fabPlane/playbridge-ps1-wireless-adapter/docs/diagrams/ps1-contact-allocation.png

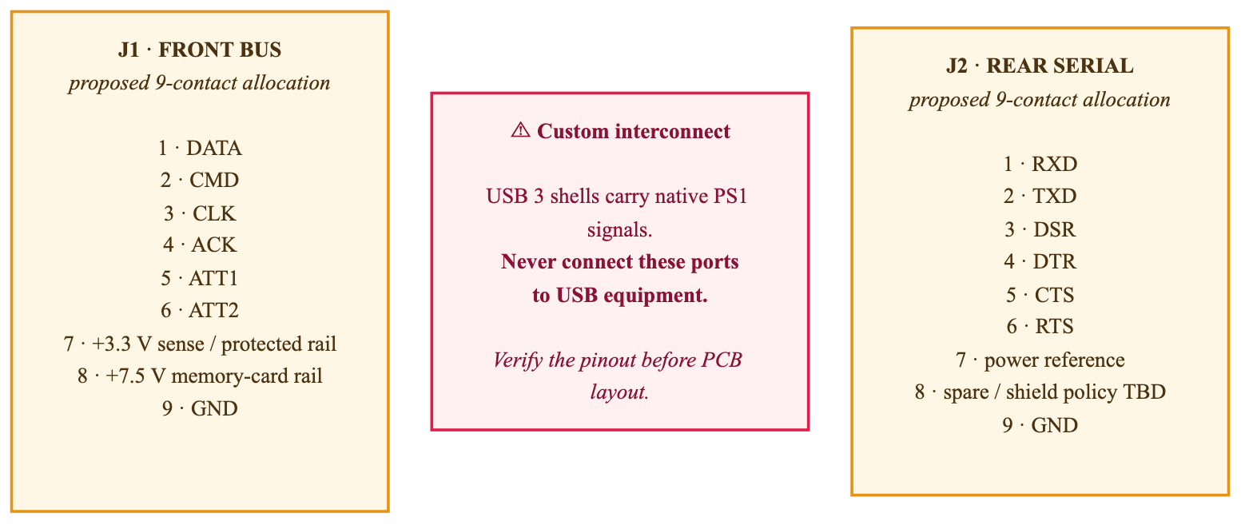
docs/diagrams/ps1-contact-allocation.png
