fabPlane/playbridge-ps1-wireless-adapter/docs/diagrams/ps1-front-harness.png

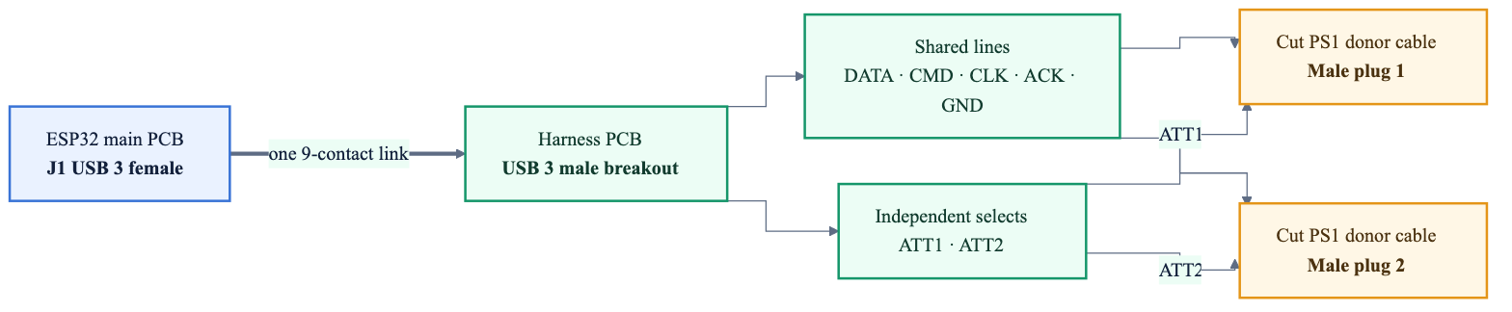
docs/diagrams/ps1-front-harness.png
