fabPlane/playbridge-ps1-wireless-adapter/docs/diagrams/ps1-modular-interconnect.png

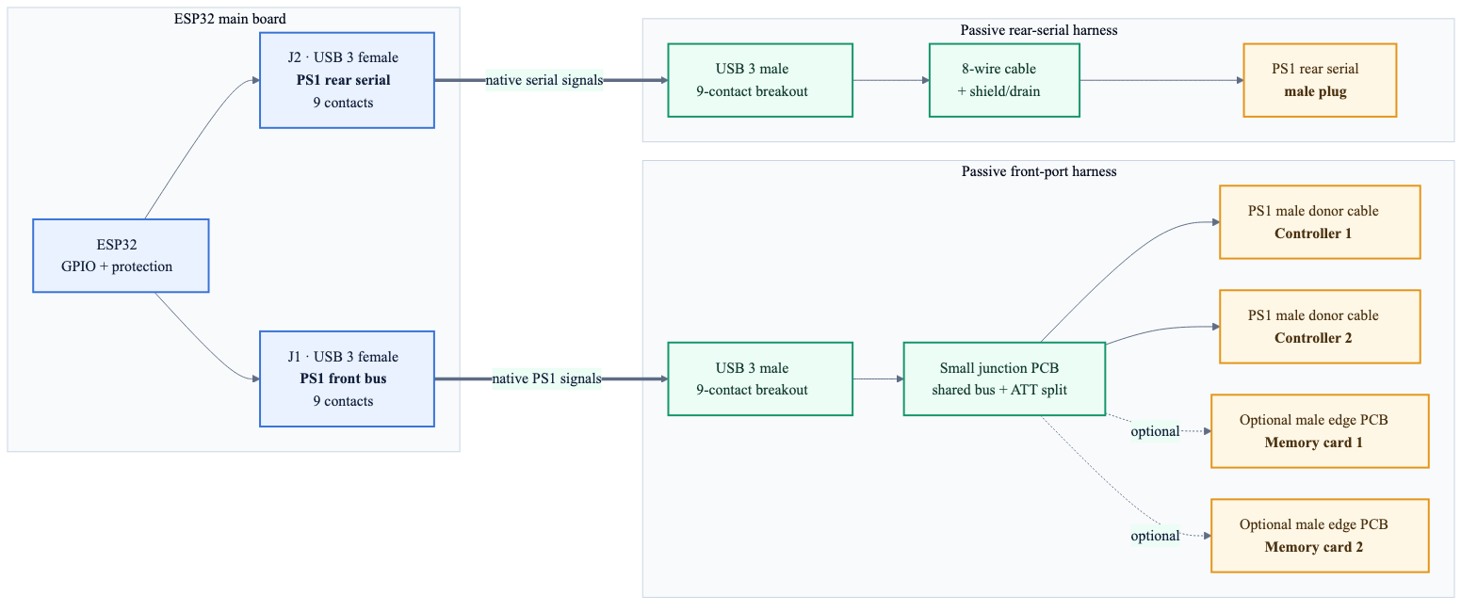
docs/diagrams/ps1-modular-interconnect.png
