fabPlane/playbridge-ps1-wireless-adapter/versions/v1-pcb-mounted-pin-array/docs/images/current/full-board-top-orthographic.png

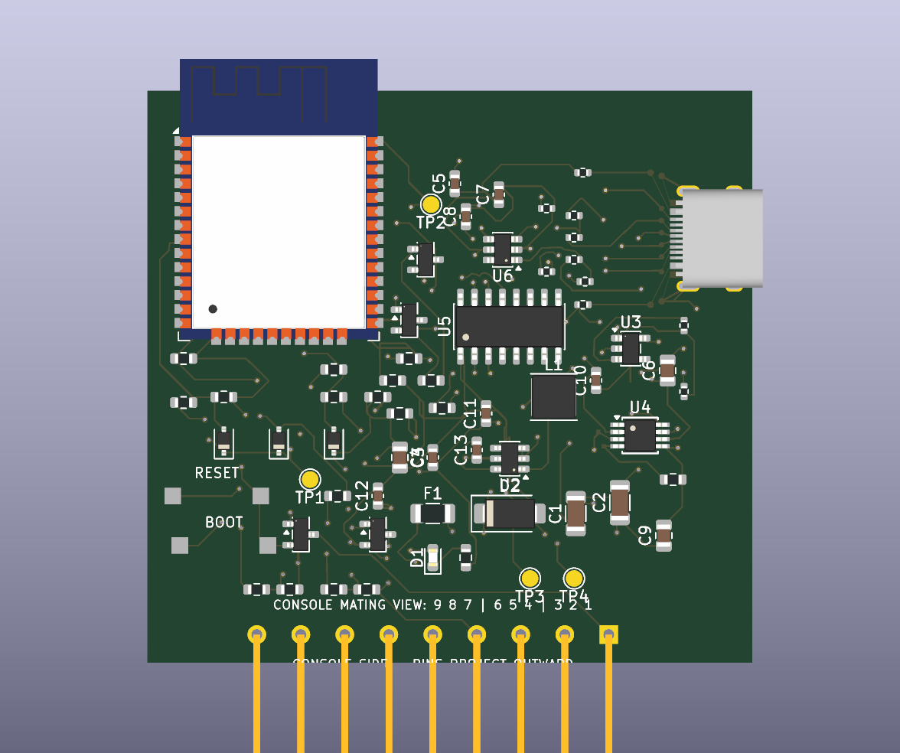
versions/v1-pcb-mounted-pin-array/docs/images/current/full-board-top-orthographic.png
