fabPlane/playbridge-ps1-wireless-adapter/versions/v1-pcb-mounted-pin-array/docs/images/current/usb-c-close-perspective.png

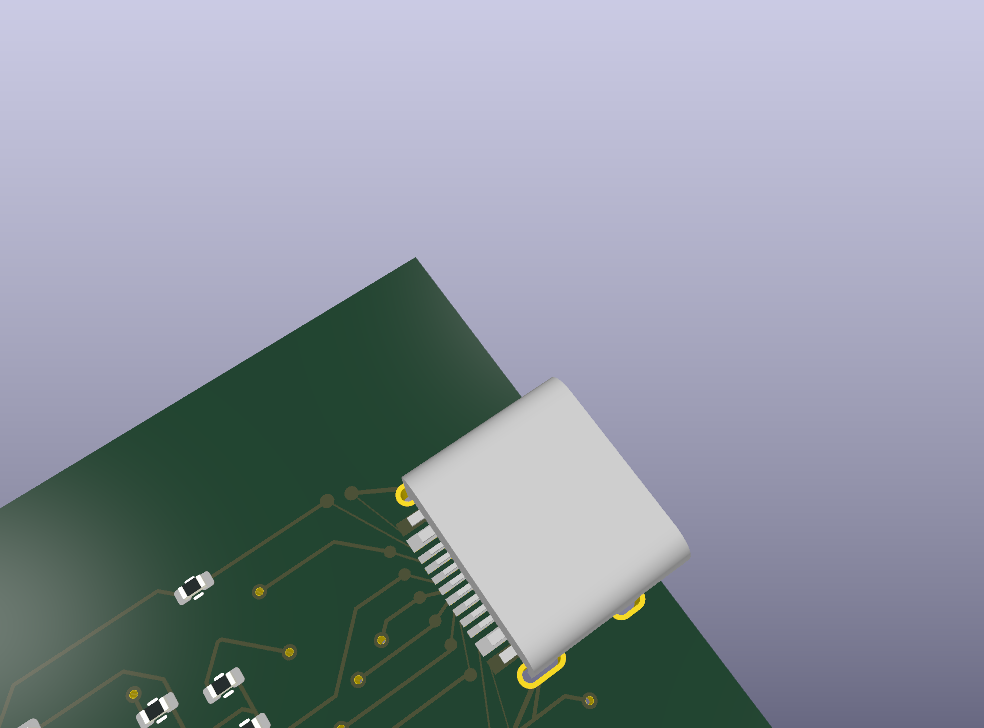
versions/v1-pcb-mounted-pin-array/docs/images/current/usb-c-close-perspective.png
