fabPlane/playbridge-ps1-wireless-adapter/versions/v1-pcb-mounted-pin-array/docs/images/current/usb-c-edge-close-up.png

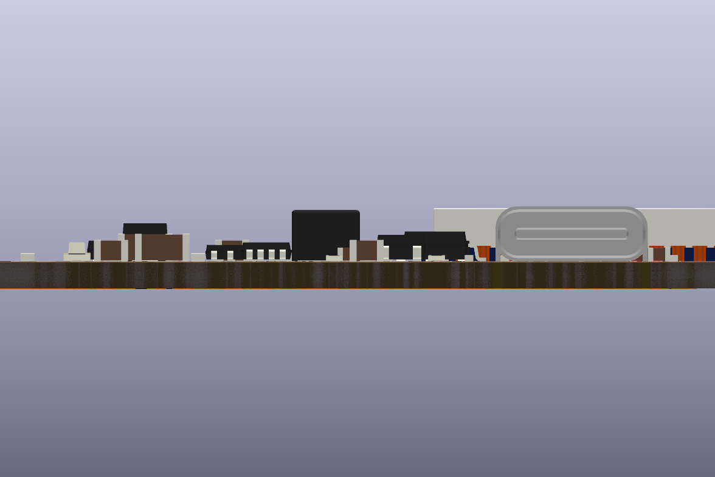
versions/v1-pcb-mounted-pin-array/docs/images/current/usb-c-edge-close-up.png
