fabPlane/playbridge-ps1-wireless-adapter/versions/v1-pcb-mounted-pin-array/references/user-photos/red-pcb-pin-layout-reference.png

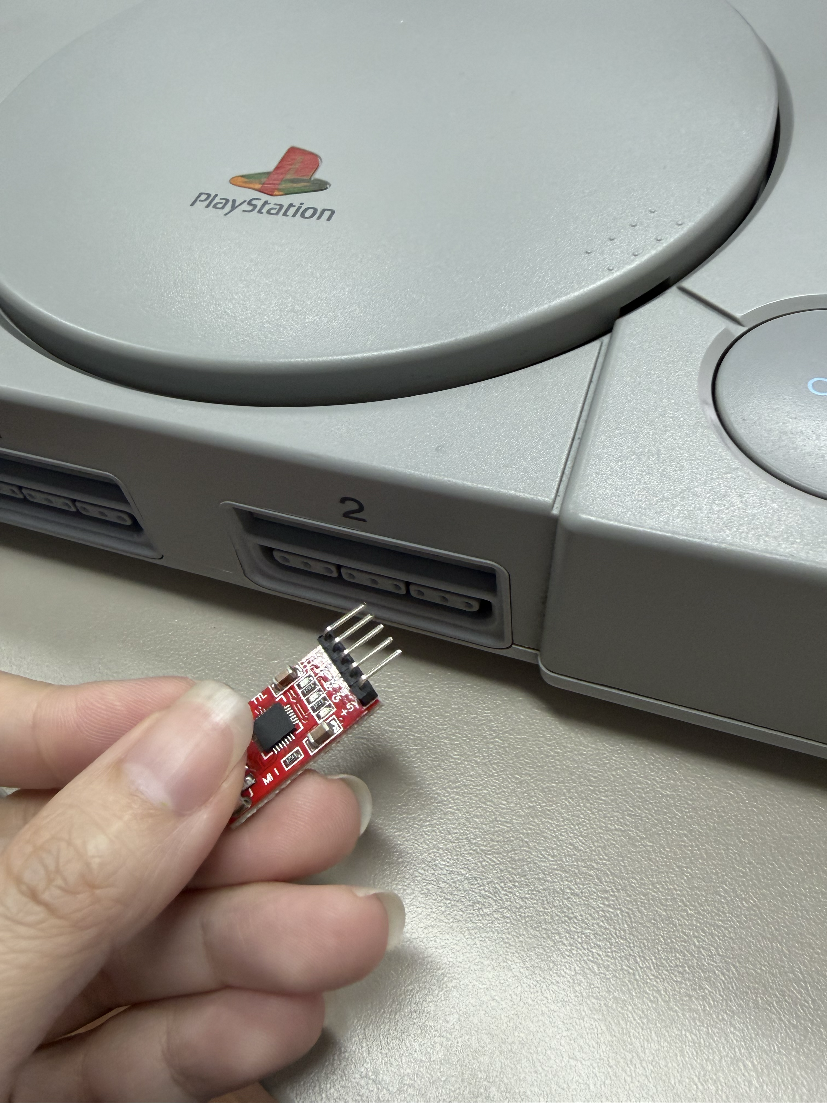
versions/v1-pcb-mounted-pin-array/references/user-photos/red-pcb-pin-layout-reference.png
