fabPlane/playbridge-ps1-wireless-adapter/versions/v1-pcb-mounted-pin-array/sketches/usb-c-orientation-reference.png

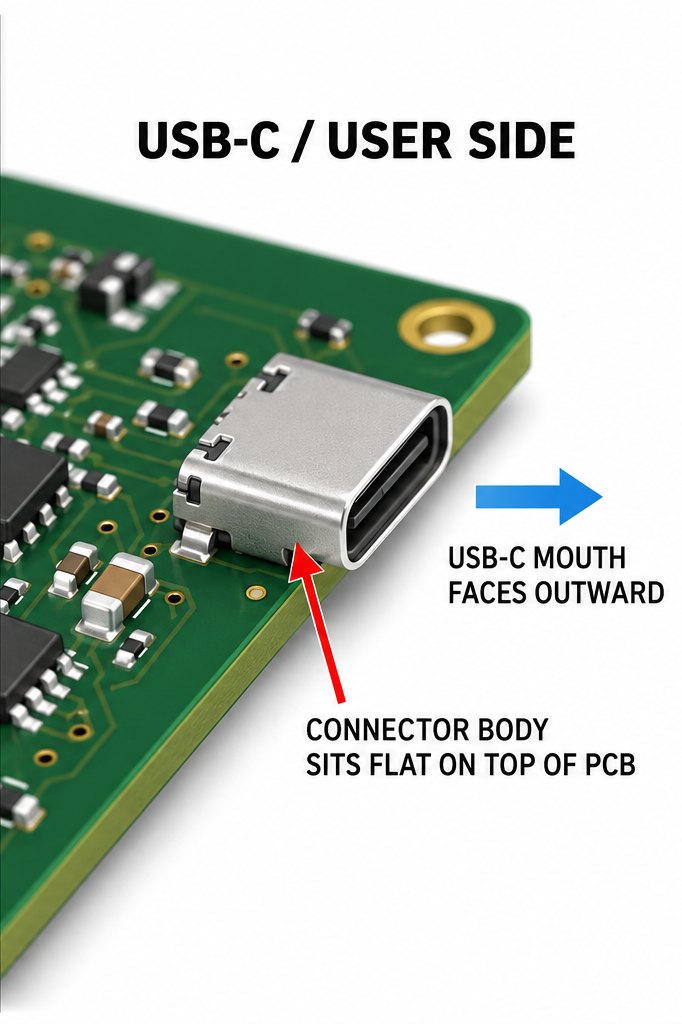
versions/v1-pcb-mounted-pin-array/sketches/usb-c-orientation-reference.png
