fabPlane/playbridge-ps1-wireless-adapter/versions/v2-donor-plug-modular-adapter/renders/kicad-technical-full-top.png

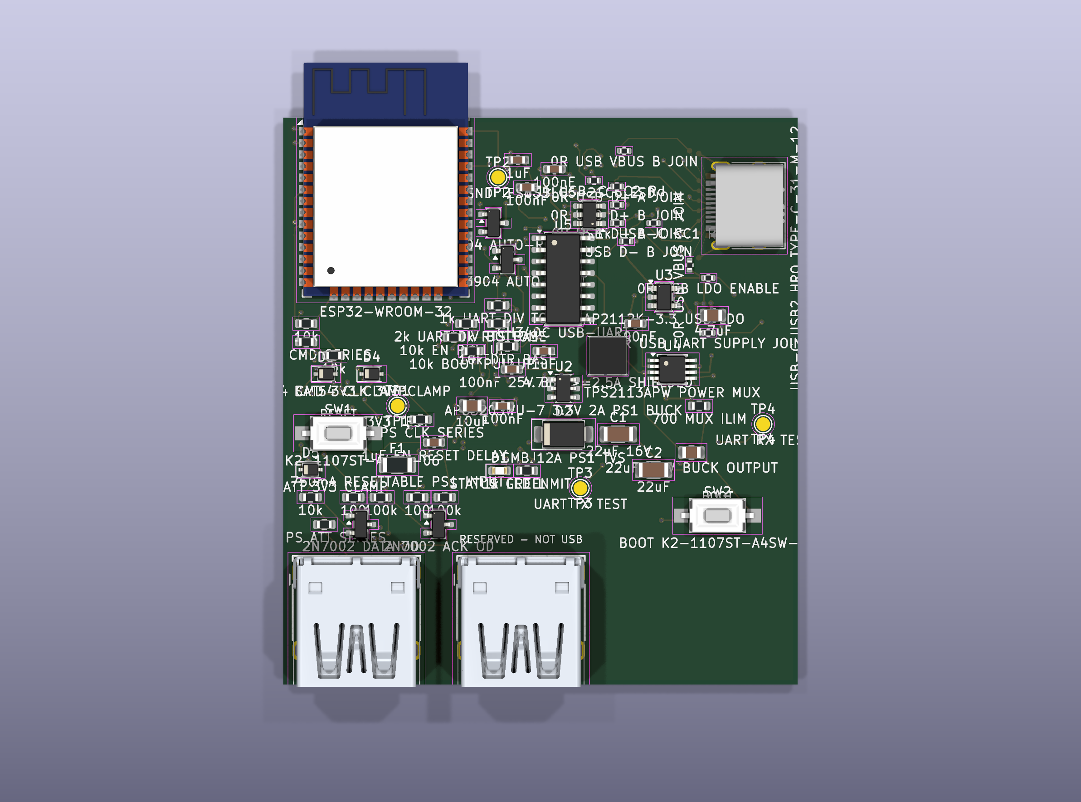
versions/v2-donor-plug-modular-adapter/renders/kicad-technical-full-top.png
