fabPlane/playbridge-ps1-wireless-adapter/versions/v2.1-status-leds-uart-debug/concepts/usb3-breakout-example.jpeg

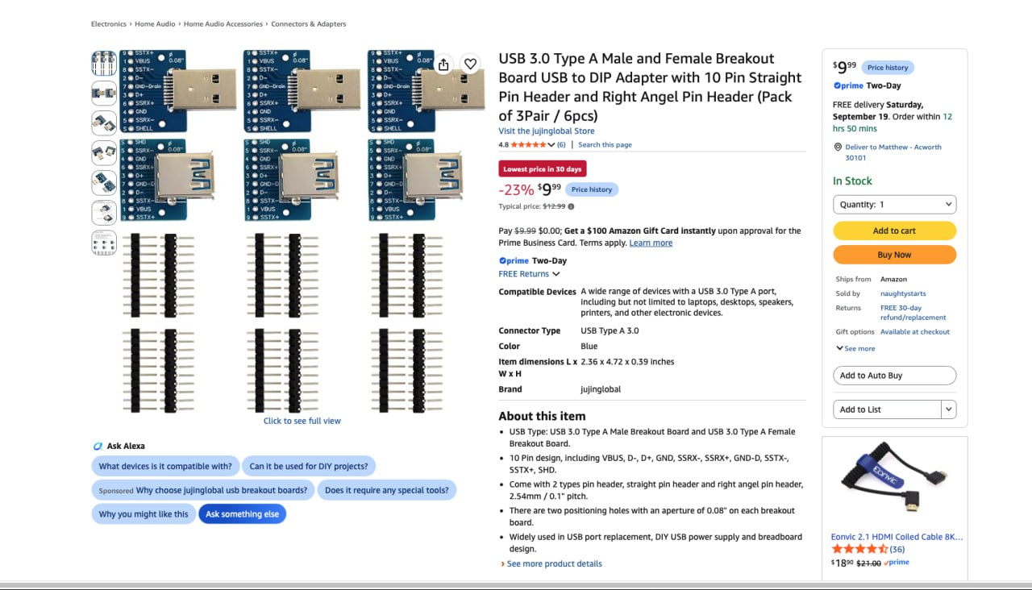
versions/v2.1-status-leds-uart-debug/concepts/usb3-breakout-example.jpeg
