fabPlane/playbridge-ps1-wireless-adapter/versions/v3.0-ps1-serial-harness/references/ps1-donor-plug/oblique-contact-view.png

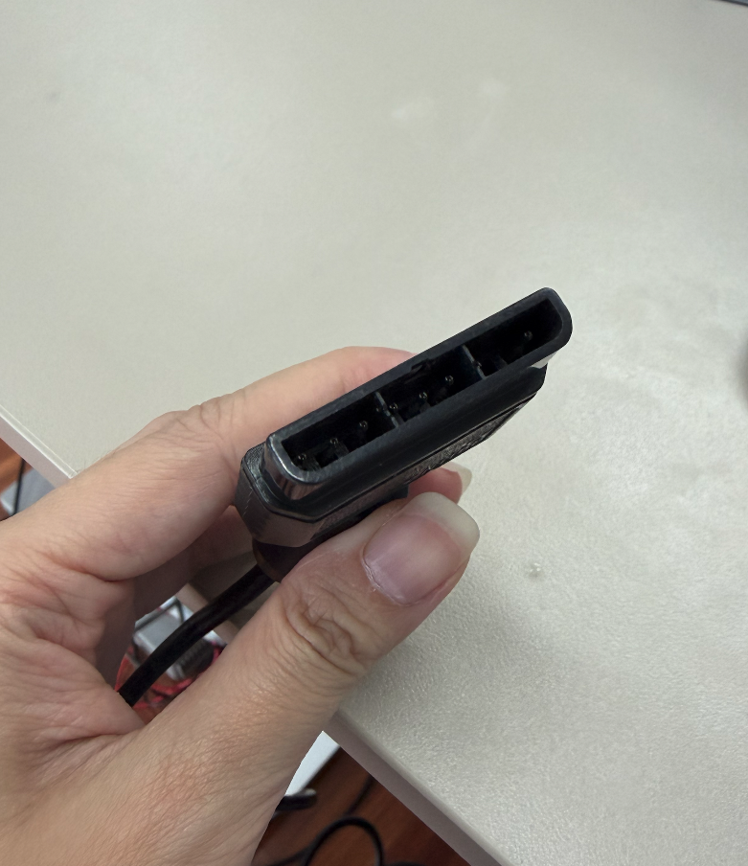
versions/v3.0-ps1-serial-harness/references/ps1-donor-plug/oblique-contact-view.png
