fabPlane/playbridge-ps1-wireless-adapter/versions/v3.0-ps1-serial-harness/renders/v3.0-populated-top.png

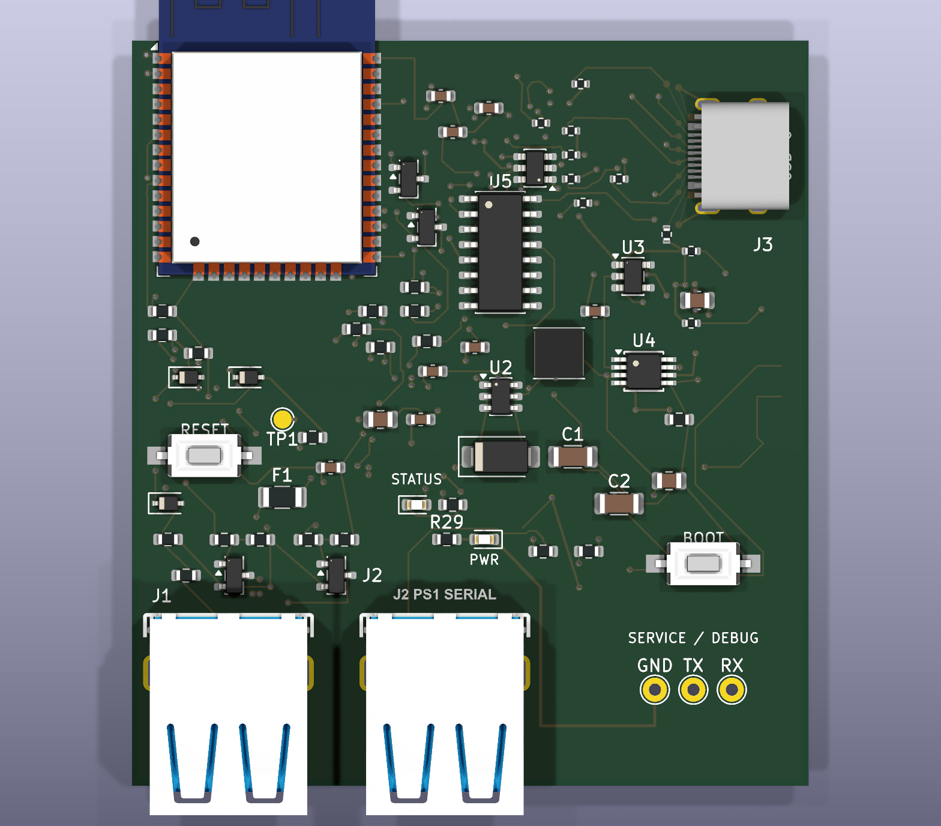
versions/v3.0-ps1-serial-harness/renders/v3.0-populated-top.png
