fabPlane/playbridge-ps1-wireless-adapter/versions/v4.1-controller-serial-bridge/renders/j1-orthographic-top.png

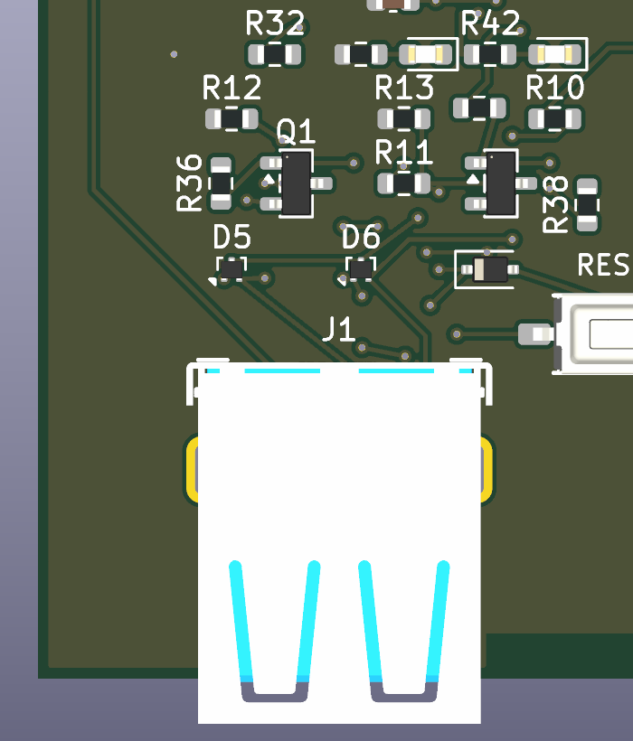
versions/v4.1-controller-serial-bridge/renders/j1-orthographic-top.png
