fabPlane/playbridge-ps1-wireless-adapter/versions/v4.1-controller-serial-bridge/renders/populated-top.png

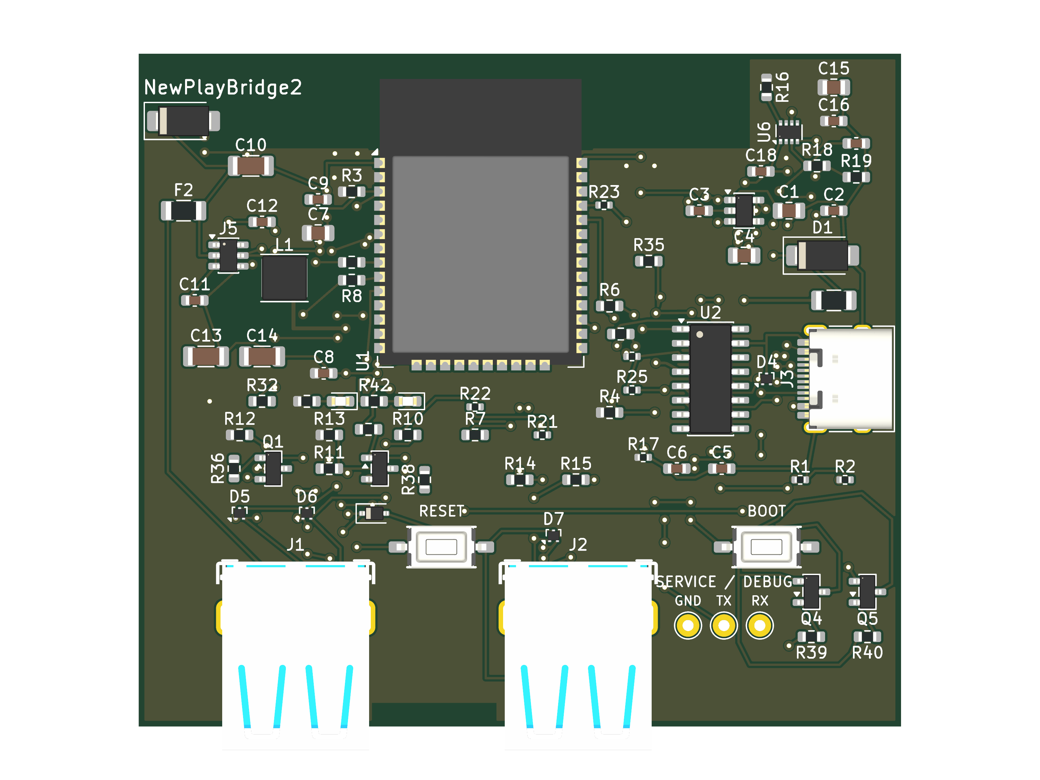
versions/v4.1-controller-serial-bridge/renders/populated-top.png
