fabPlane/playbridge-ps1-wireless-adapter/versions/v3.0-ps1-serial-harness/reports/evidence/poc-node32lite-wiring.png

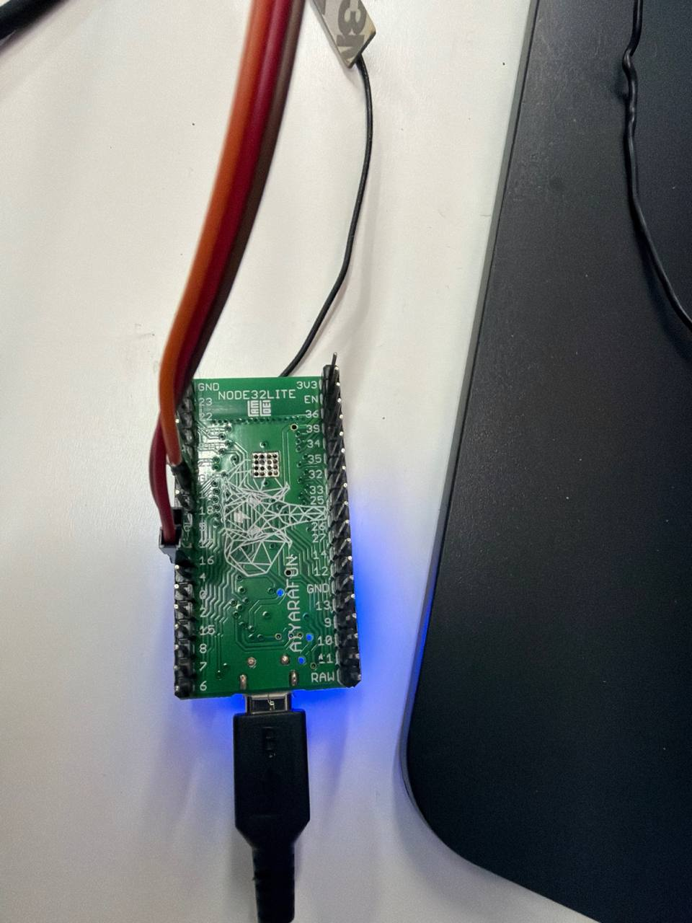
versions/v3.0-ps1-serial-harness/reports/evidence/poc-node32lite-wiring.png
