fabPlane/playbridge-ps1-wireless-adapter/versions/v2.1-status-leds-uart-debug/renders/service-debug-full-top.png

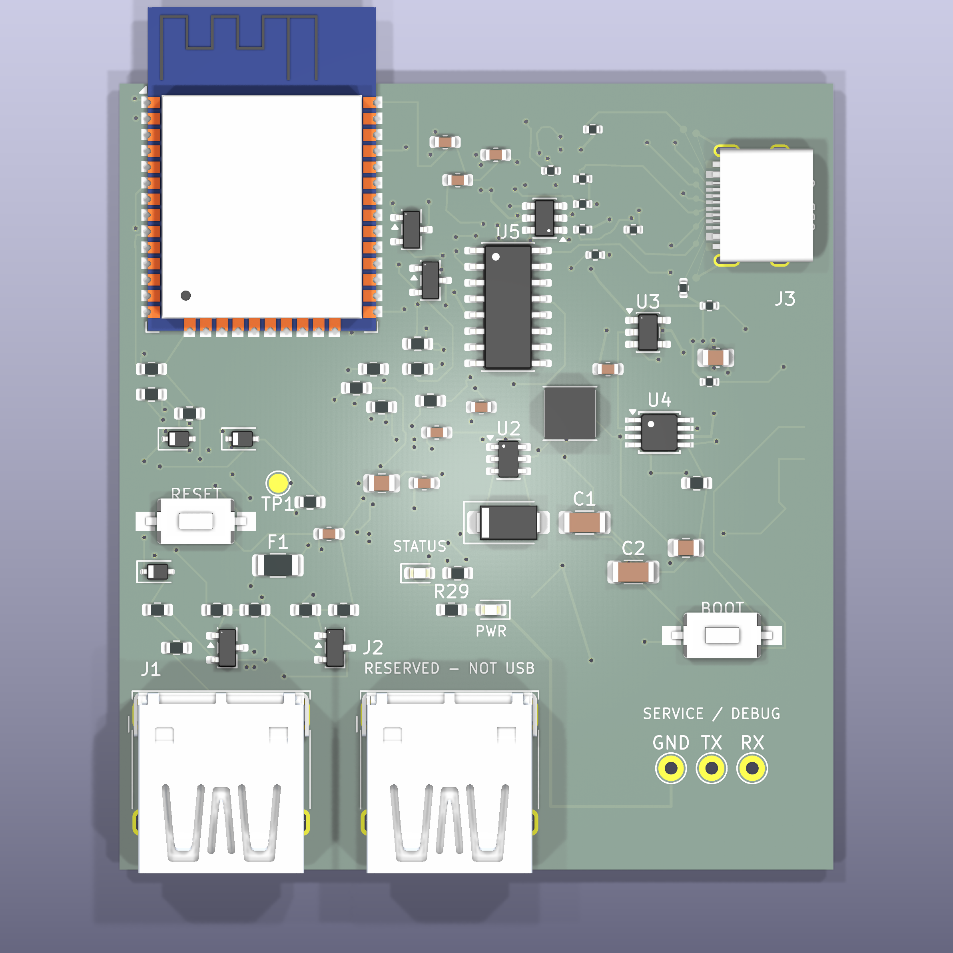
versions/v2.1-status-leds-uart-debug/renders/service-debug-full-top.png
